brainsmoke/chiral_sphere/doc/wiring.scad

$fn=100;
e=.001;

r=100;
w=8;
h=6;

/*
 * alpha: the regular spherical triangles' great-circle arc (edge-length)
 * beta:  the regular spherical pentagons' great-circle arc (edge-length)
 *
 * A: the triangles' corner arc
 * B: the pentagons' corner arc
 * A+B = tau/2
 *
 * alpha = 2*beta
 * cos (alpha) = 1 / (1-cos(A)) - 1
 * cos (beta)  = (phi + 1) / (1-cos(B)) - 1
 * cos (beta)  = (phi + 1) / (1+cos(A)) - 1
 *
 * let x = cos(A)
 *
 * 1 / (1-x) -1 = 2 * ( (phi + 1)/(1+x) - 1 )^2 - 1
 *
 * x^3+(-2*phi-1/2)x^2+(3*phi+2)x + (-phi-1/2) = 0
 */

phi=(1+sqrt(5))/2;
cuberoot=pow(118*phi+85+6*sqrt(1173*phi+729), 1/3);
cos_A=(1/6)*(4*phi+1) +
      (1/6)*(12*phi+7)/cuberoot -
      (1/6)*cuberoot;
sin_A=sqrt(1-cos_A*cos_A);

A=acos(cos_A);

cos_alpha=1/(1-cos_A)-1;
alpha=acos(cos_alpha);

module arc(r, w, h)
{
    rotate_extrude(angle=alpha*3/2)
    translate([r-h/2,0])square([h,w],center=true);
}

module chopped(r,w,h)
{
        for (i = [0, alpha*3/2])
        rotate([0,0,i])
        rotate([A,0,0])
        translate([r,0,0])
        cube([2*(w+h),2*(w+h),w-e],center=true);
}

module chopped_arc(r,w,h)
{
    difference()
    {
        arc(r,w,h);
        chopped(r,w,h);
    }
}

module wiring(r, w, h)
{
    difference()
    {
        union()
        {
        color([1,0,0])rotate_extrude(angle=alpha*3/2)
            translate([r-h/2,-w/3])square([h,w/10],center=true);
        color([1,1,1])rotate_extrude(angle=alpha*3/2)
            translate([r-h/2,0])square([h,w/10],center=true);
        color([0,0,0])rotate_extrude(angle=alpha*3/2)
            translate([r-h/2,w/3])square([h,w/10],center=true);
        }
        chopped(r,w,h);
    }
}

module spherical_arc(r,w,h)
{
    intersection()
    {
        chopped_arc(r+h,w,h+r);
        difference()
        {
            sphere(r);
            sphere(r-h);
        }
    }
}

module arrow(l, w, h)
{
    translate([0,l/2,0])cube([h,l,w],center=true);
    translate([0,l,0])rotate([90,0,90])cylinder(h,w*2,w*2,center=true,$fn=3);
}

near=true;
far=false;

wiring_config = [

near,  far, near, near,
near, near,  far,  far,
near, near,  far, near,

];

wiring_colors = [
0, 1, 0, 1,
0, 1, 0, 1,
0, 1, 0, 1,
];

color_lookup = [
    [ [1,0,0], [0,0,0] ],
    [ [0,0,0], [1,0,0] ],
];

module joint(l, w, h, o1, o2)
{
    w0=o1+w/2;
    w1=o1-w/2;
    w2=o2+w/2;
    w3=o2-w/2;
    half_w = w/2;
    joint_poly=[
 [ -l,                           w1 ],
 [ -l,                           w0 ],
 [ (cos_A*w0-w2)/sin_A    , w0 ],
 [  cos_A*l -sin_A*w2, l*sin_A +w2*cos_A ],
 [  cos_A*l -sin_A*w3, l*sin_A +w3*cos_A ],
 [ (cos_A*w1-w3)/sin_A,       w1 ],
];
    translate([h,0,0])color([0,.6,0])rotate([-90,0,90])linear_extrude(h)polygon(joint_poly); 
}

module joint_wiring(facet_r, w, h, type, color_a, color_b)
{
    if (type==near)
    {
        color(color_a)joint(8,1,h,2,2);
        color(color_b)joint(8,1,h,-2,-2);
    }
    if (type==far)
    {
        color(color_a)joint(8,1,h,2,-2);
        color(color_b)joint(8,1,h-e,-2,2);
    }

}

module step_x()
{
    rotate([0,0,alpha/2])rotate([-A,0,0])
    children();
}

module step_y()
{
    rotate([0,0,3*alpha/2])rotate([180,0,0])
    children();
}

module penta()
{
    $penta_count=is_undef($penta_count)?0:$penta_count;
    children();
    step_x(){
        $penta_count=$penta_count+1;
        children();
        step_x(){
            $penta_count=$penta_count+1;
            children();
            step_x(){
                $penta_count=$penta_count+1;
                children();
                step_x(){
                    $penta_count=$penta_count+1;
                    children();
                }
            }
        }
    }
}

module extend()
{
    $count=is_undef($count)?0:$count;
    children();
    step_y()step_x(){
        $count=$count+1;
        children();
        step_x(){
            $count=$count+1;
            children();
            step_x(){
                $count=$count+1;
                children();
                step_y()step_x(){
                    $count=$count+1;
                    children();
                    step_y()step_x()step_x()step_x()step_x(){
                        $count=$count+1; 
                        children();
                    }
                }
            }        
        }
    }
}

module ball()
{
    penta()extend()children();
}

module joint_points()
{
    $count = $count * 2;
    rotate([0,0,alpha/2])
    {
        children();
        rotate([0,0,alpha/2])rotate([180,0,0])
        {
            $count = $count + 1;
            children();
        }
    }
}


ball(){
    color([.8,.8,.8])chopped_arc(r,w,h);
    wiring(r+1+w/10,w,w/10);

    joint_points()
    translate([r-3,-(1-cos_A)/sin_A*7,-7])
    {
        color([0,.6,0])joint(8, 6, 1, 0, 0);
        translate([1,0,0])
        joint_wiring(8, 6, 1, wiring_config[$count],
                     color_lookup[wiring_colors[$count]][0],
                     color_lookup[wiring_colors[$count]][1]);
    }
}

extend()
{
    chopped_arc(r+1,w,1);
    color([0,1,0])translate([r+2,5,0])arrow(10,w/3,3);
    color([0,0,.8])translate([r+2,-8,-w*.6])rotate([90,0,90])linear_extrude(1)text(str($count));
}

penta()
{
    color([0,1,1])translate([r+10,0,0])rotate([180,0,90])linear_extrude(1)text(str("strip ",$penta_count));
}

rotate([0,0,3*alpha/4])
{
    color("red")translate([r+80,-5,0])rotate([0,180,0])text("this side up");
}
